Ordep-42/LEGO-HOTAS/assets/Hotas-Schema/Hotas-Schema.kicad_pcb

## KiCad design Expression Pedal USB-Adapter/EXP_P_USB_Adapter/EXP_P_USB_Adapter.kicad_sch

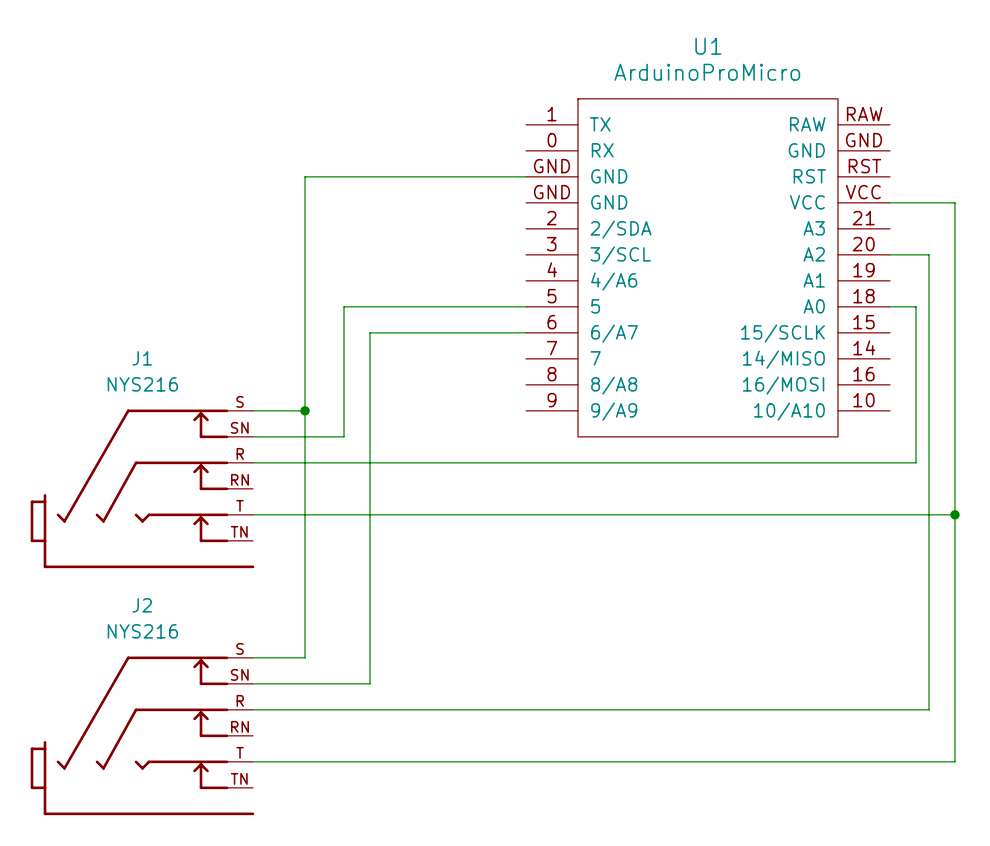
[picture p3: schematic EXP_P_USB_Adapter.kicad_sch]

Parts:
J1, J2: NYS216; REAN_NYS216; PARTREV 2015.05.27
U1: ArduinoProMicro

Connections:
unnamed: J1.R, U1.18 (A0)
unnamed: J1.S, J2.S, U1.GND
unnamed: J1.SN, U1.5
unnamed: J1.T, J2.T, U1.VCC
unnamed: J2.R, U1.20 (A2)
unnamed: J2.SN, U1.6 (6/A7)
